gerb-ster/CoronDS8-Clone/images/IMG_1323.jpeg

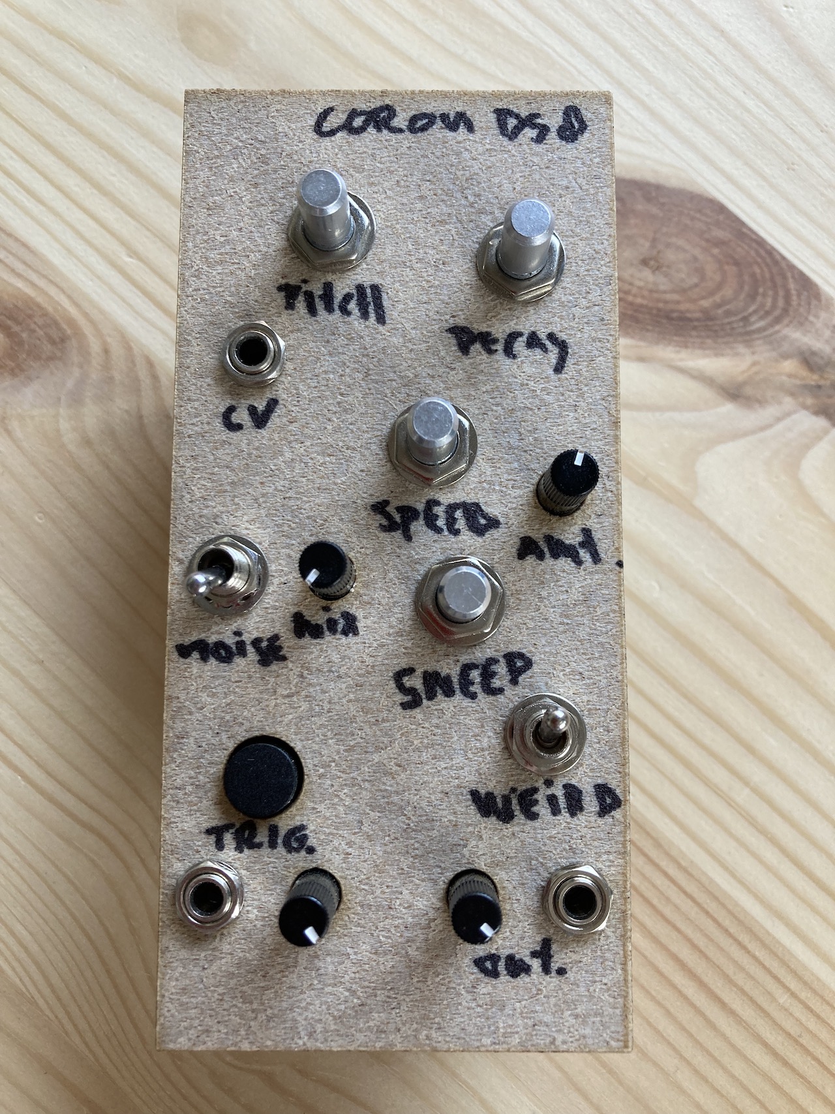
images/IMG_1323.jpeg
