gerb-ster/CoronDS8-Clone/images/IMG_1326.jpeg

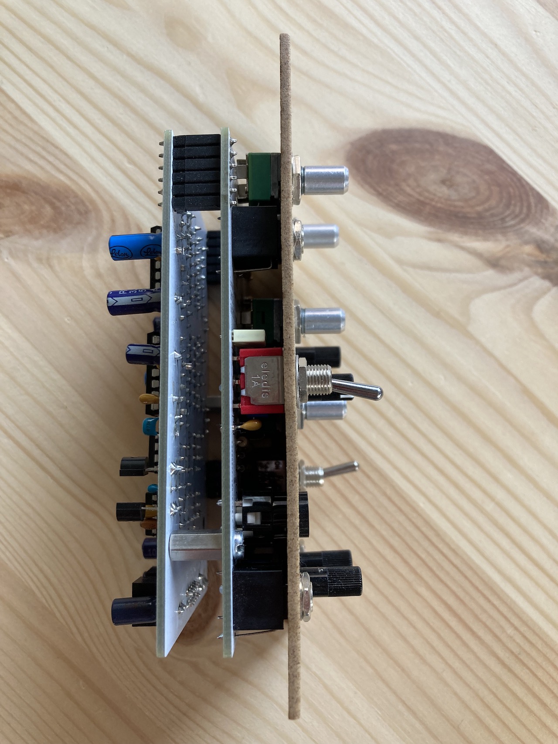
images/IMG_1326.jpeg
