gerb-ster/CoronDS8-Clone/images/IMG_1328.jpeg

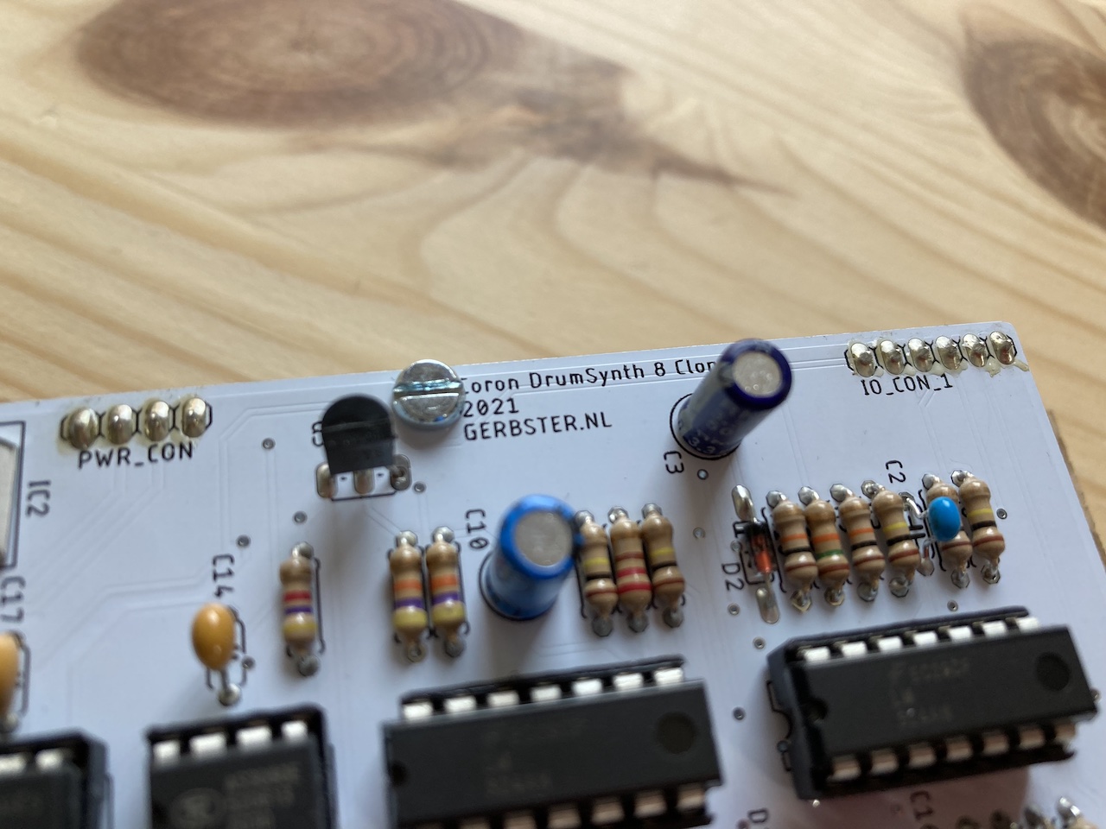
images/IMG_1328.jpeg
